sdp8483/card_lights/firmware/card_lights_touch_charlieplex/random.c

/**
 * Copyright (c) 2017, Łukasz Marcin Podkalicki <lpodkalicki@gmail.com>
 * Lightweight library of 16 bit random number generator based on LFSR.
 */

#include "random.h"

static uint16_t random_number = 0xabcd;

static uint16_t lfsr16_next(uint16_t n) {
	return (n >> 0x01U) ^ (-(n & 0x01U) & 0xB400U);
}


void random_init(uint16_t seed) {
	random_number = seed;
}


uint16_t random(void) {
	return (random_number = lfsr16_next(random_number));
}
